DeanElec/Compact-high-efficiency-illumination-systems-for-in-orbit-microscopy/Lens-characterisation/resolving_power_and_chromatic_aberration/logistical_fit_red_green_blue_spectrums.PNG

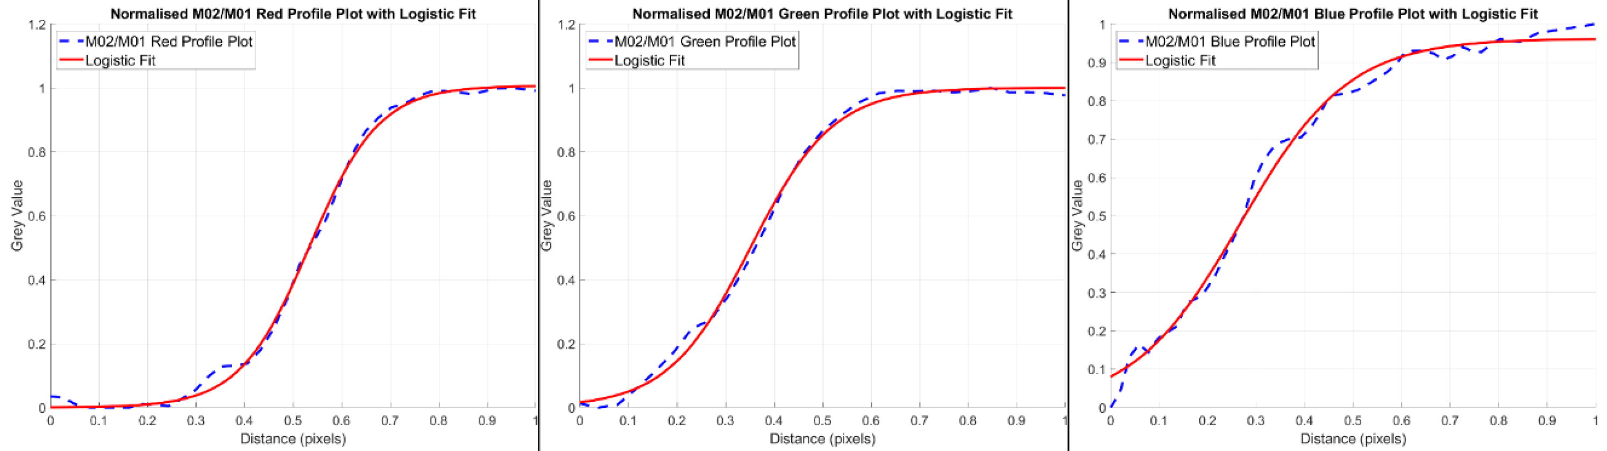
Lens-characterisation/resolving_power_and_chromatic_aberration/logistical_fit_red_green_blue_spectrums.PNG
