DeanElec/Compact-high-efficiency-illumination-systems-for-in-orbit-microscopy/Microscope_CAD_Designs/Microscope_CAD_Design_V2_Files/Step_Files/New_Spur_and_Rod v4.step

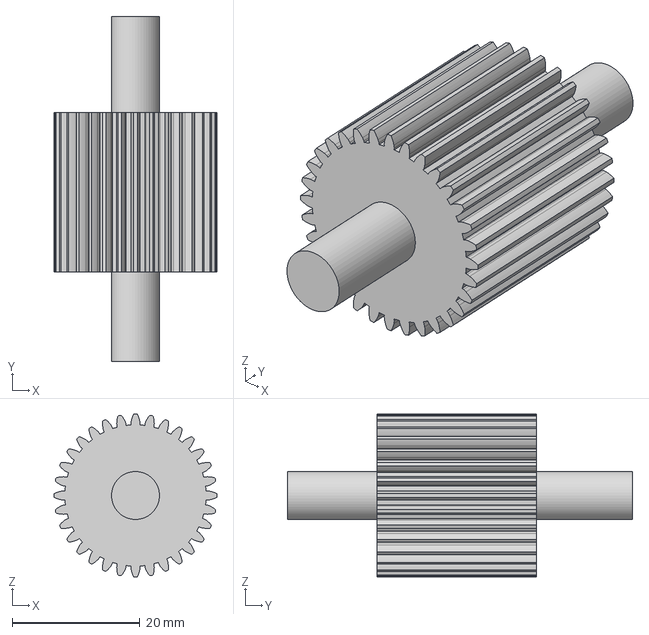
[picture p23: CAD file, 2024-05-28]
Microscope_CAD_Designs/Microscope_CAD_Design_V2_Files/Step_Files/New_Spur_and_Rod v4.step
25.5 x 54.0 x 25.5 mm
