DeanElec/Compact-high-efficiency-illumination-systems-for-in-orbit-microscopy/Microscope_CAD_Designs/Microscope_Stand_V1/Microscope_CAD_Design_V1_Files/Step_Files/Camera_Holder v3.step

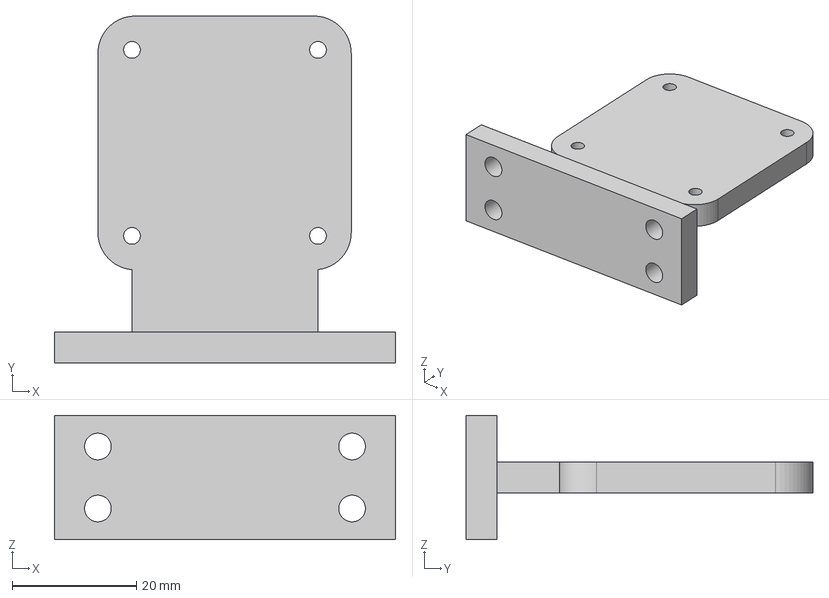
[picture p24: CAD file, 2024-05-28]
Microscope_CAD_Designs/Microscope_Stand_V1/Microscope_CAD_Design_V1_Files/Step_Files/Camera_Holder v3.step
55.0 x 56.0 x 20.0 mm
