DeanElec/Compact-high-efficiency-illumination-systems-for-in-orbit-microscopy/Microscope_CAD_Designs/Microscope_Stand_V1/Microscope_CAD_Design_V1_Files/Step_Files/Base Plate Dimensions v2.step

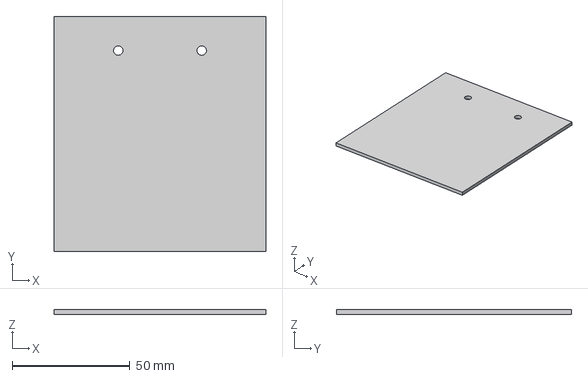
[picture p25: CAD file, 2024-05-28]
Microscope_CAD_Designs/Microscope_Stand_V1/Microscope_CAD_Design_V1_Files/Step_Files/Base Plate Dimensions v2.step
90.0 x 100.0 x 2.00 mm
