DeanElec/Compact-high-efficiency-illumination-systems-for-in-orbit-microscopy/Lens-characterisation/general_lens_characterisation_parameters/Lens kit chacterisation graph (2).png

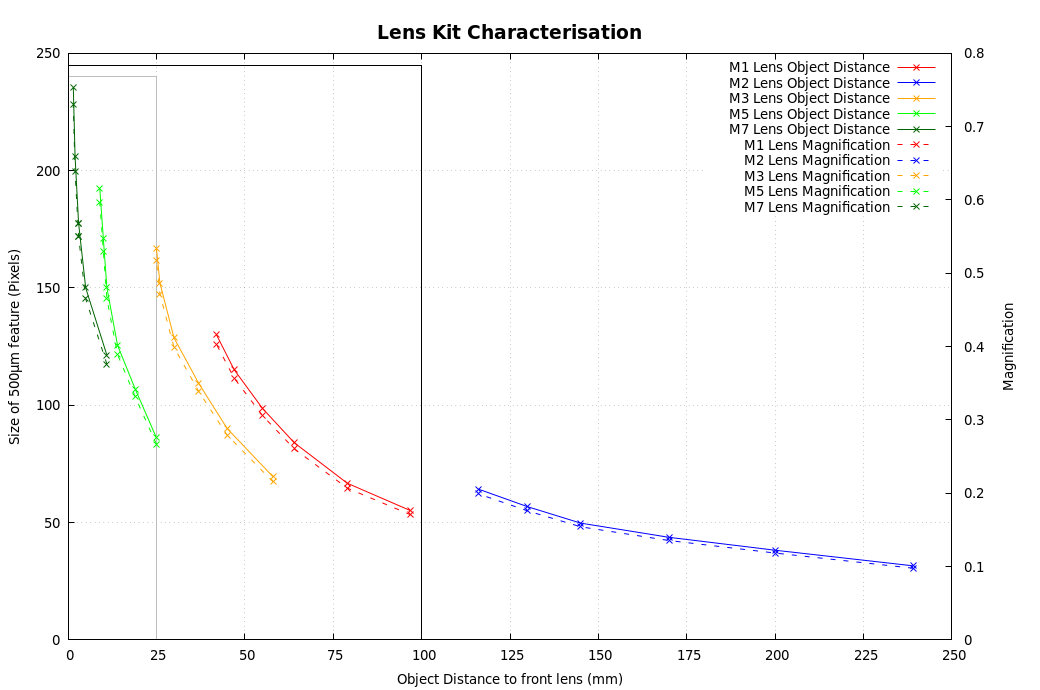
Lens-characterisation/general_lens_characterisation_parameters/Lens kit chacterisation graph (2).png
