DeanElec/Compact-high-efficiency-illumination-systems-for-in-orbit-microscopy/Lens-characterisation/general_lens_characterisation_parameters/Lens_Data_Object_Distance_vs_Measured_FOV.png

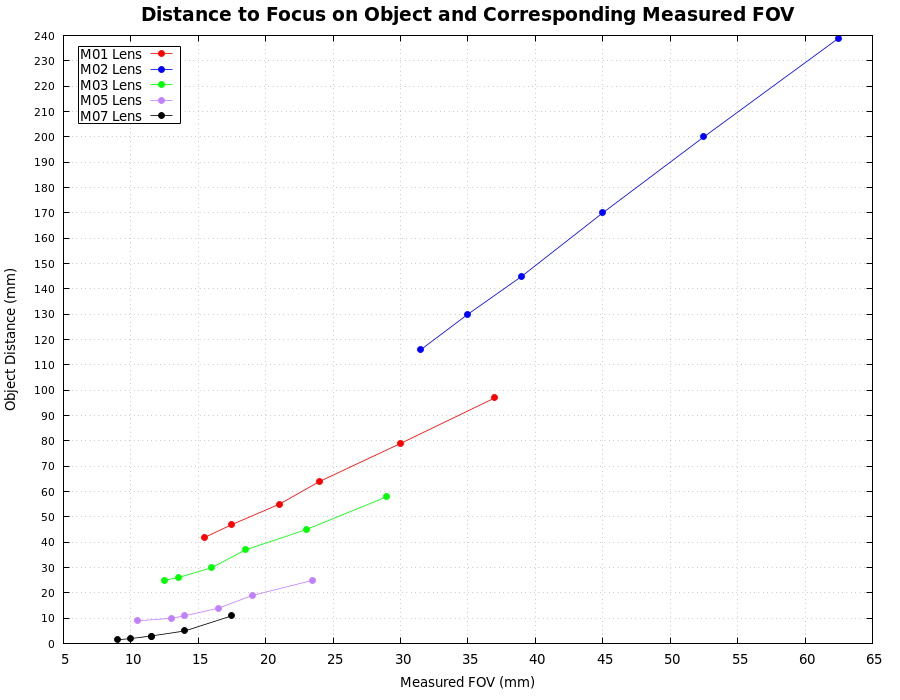
Lens-characterisation/general_lens_characterisation_parameters/Lens_Data_Object_Distance_vs_Measured_FOV.png
