DeanElec/Compact-high-efficiency-illumination-systems-for-in-orbit-microscopy/Lens-characterisation/general_lens_characterisation_parameters/linegraph_with_markers.png

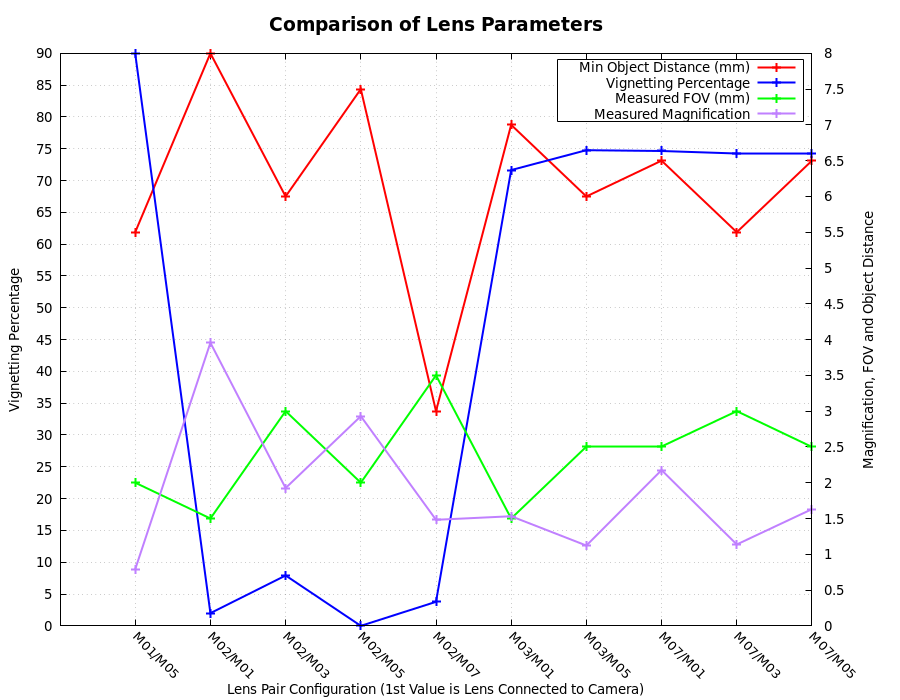
Lens-characterisation/general_lens_characterisation_parameters/linegraph_with_markers.png
