DeanElec/Compact-high-efficiency-illumination-systems-for-in-orbit-microscopy/Lens-characterisation/general_lens_characterisation_parameters/magnification_heatmap.png

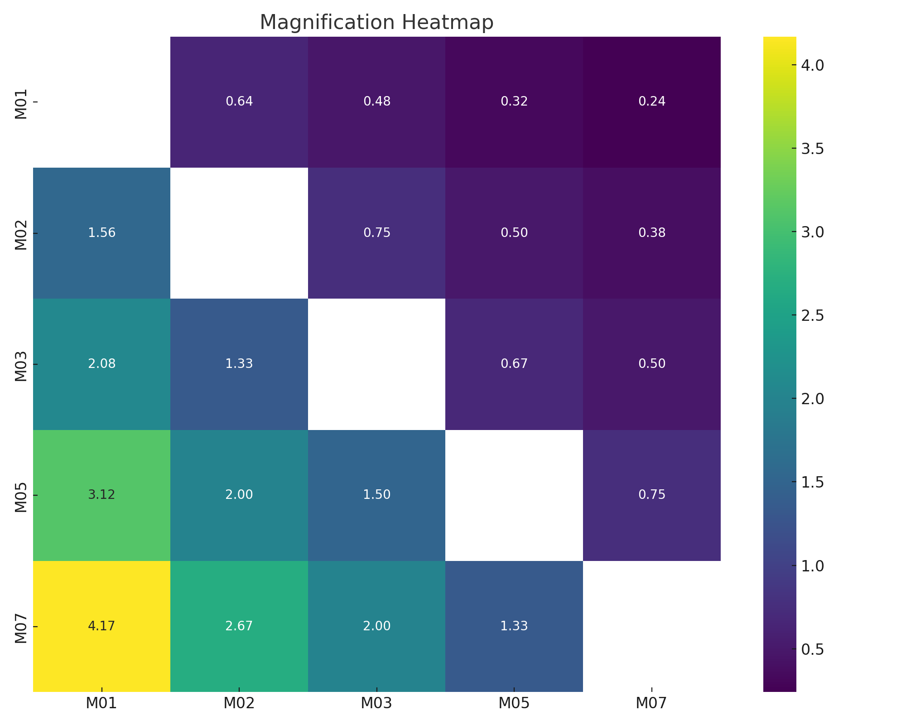
Lens-characterisation/general_lens_characterisation_parameters/magnification_heatmap.png
