DeanElec/Compact-high-efficiency-illumination-systems-for-in-orbit-microscopy/Lens-characterisation/light_transmission_efficiency/Capture.PNG

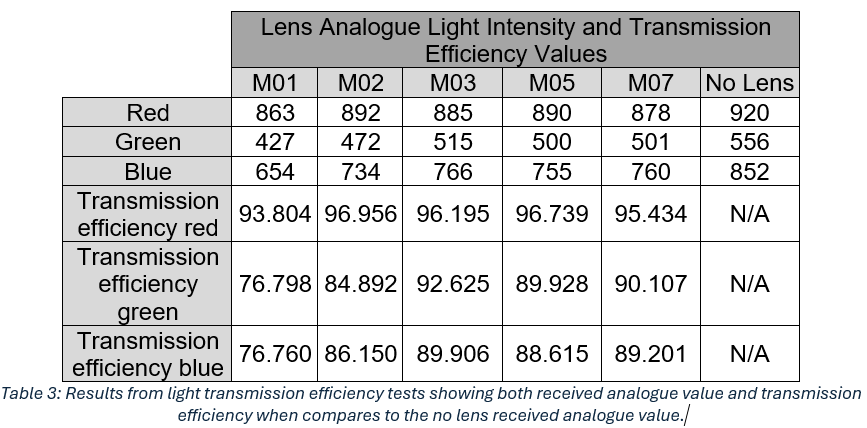
Lens-characterisation/light_transmission_efficiency/Capture.PNG
