DeanElec/Compact-high-efficiency-illumination-systems-for-in-orbit-microscopy/Lens-characterisation/light_transmission_efficiency/Internal_on_mount_side_of_lens_that_houses_LDR.png

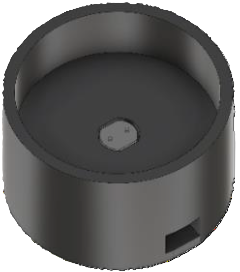
Lens-characterisation/light_transmission_efficiency/Internal_on_mount_side_of_lens_that_houses_LDR.png
