DeanElec/Compact-high-efficiency-illumination-systems-for-in-orbit-microscopy/Lens-characterisation/resolving_power_and_chromatic_aberration/M02_M01_Profile_Plots.png

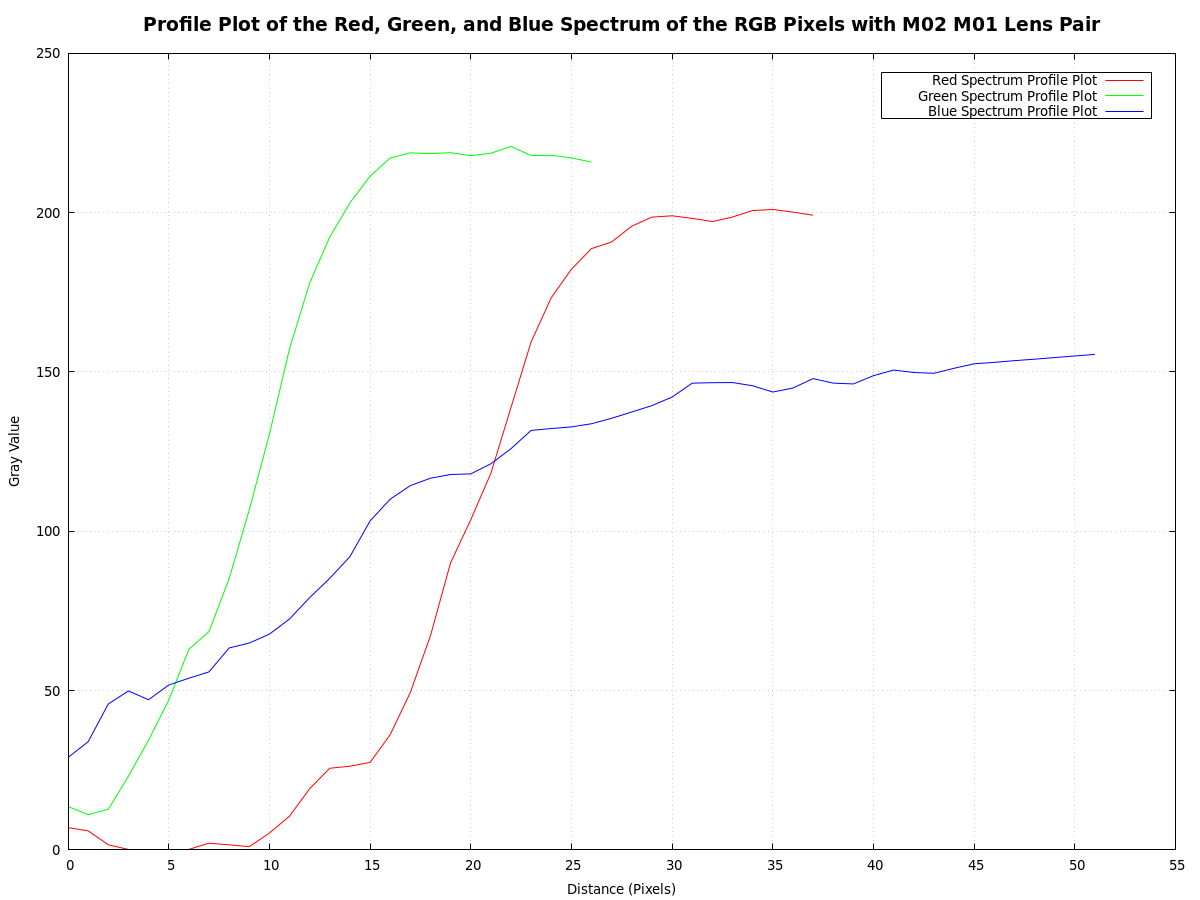
Lens-characterisation/resolving_power_and_chromatic_aberration/M02_M01_Profile_Plots.png
