DeanElec/Compact-high-efficiency-illumination-systems-for-in-orbit-microscopy/Lens-characterisation/resolving_power_and_chromatic_aberration/Parameter_of_RGB_Pixels_Samsung_Tab_S6_Lite_with_M02_M01_Lens_Pair.PNG

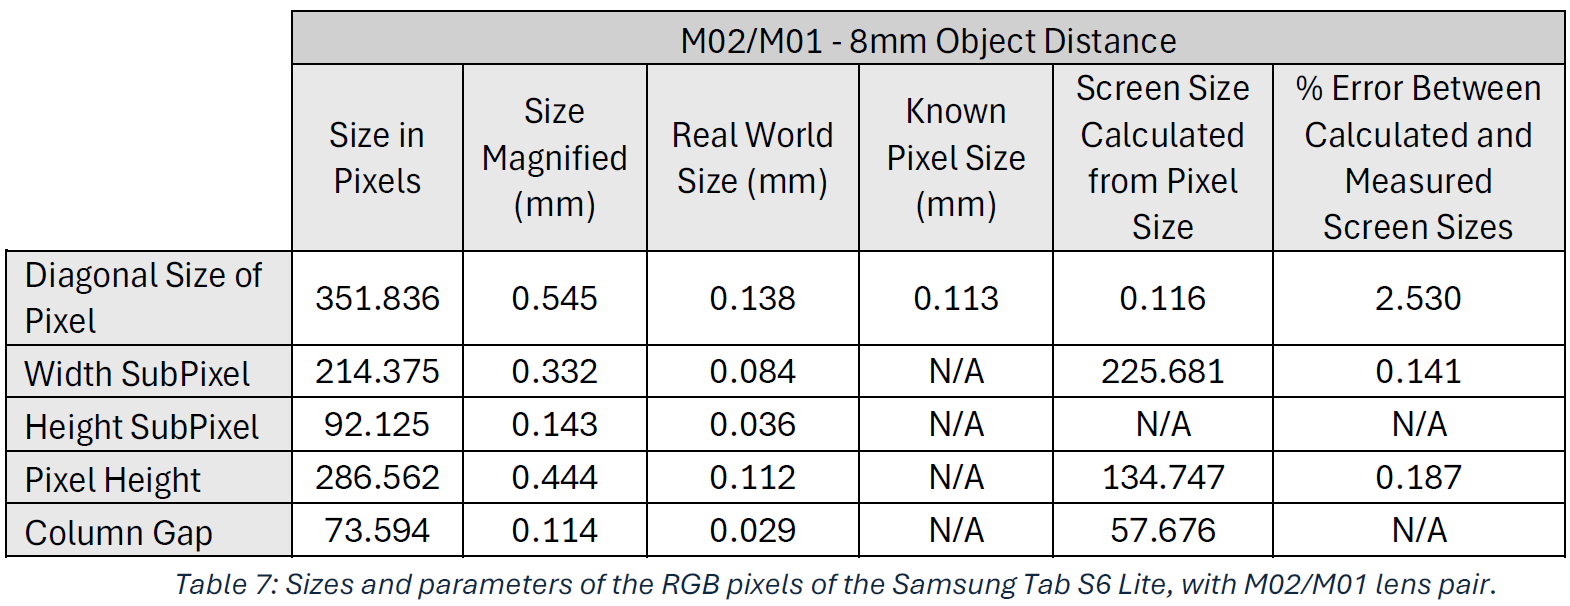
Lens-characterisation/resolving_power_and_chromatic_aberration/Parameter_of_RGB_Pixels_Samsung_Tab_S6_Lite_with_M02_M01_Lens_Pair.PNG
