DeanElec/Compact-high-efficiency-illumination-systems-for-in-orbit-microscopy/Lens-characterisation/resolving_power_and_chromatic_aberration/resolving_power_of_each_lens_config.PNG

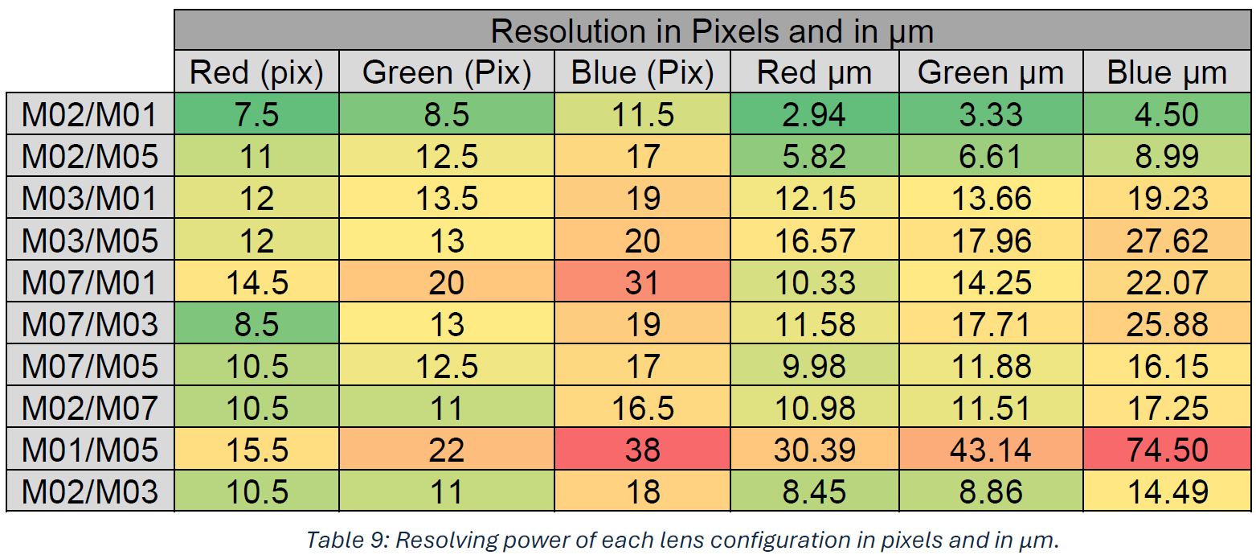
Lens-characterisation/resolving_power_and_chromatic_aberration/resolving_power_of_each_lens_config.PNG
