DeanElec/Compact-high-efficiency-illumination-systems-for-in-orbit-microscopy/Lens-characterisation/resolving_power_and_chromatic_aberration/summarised_rise_coefficent_from_logistical_fit.PNG

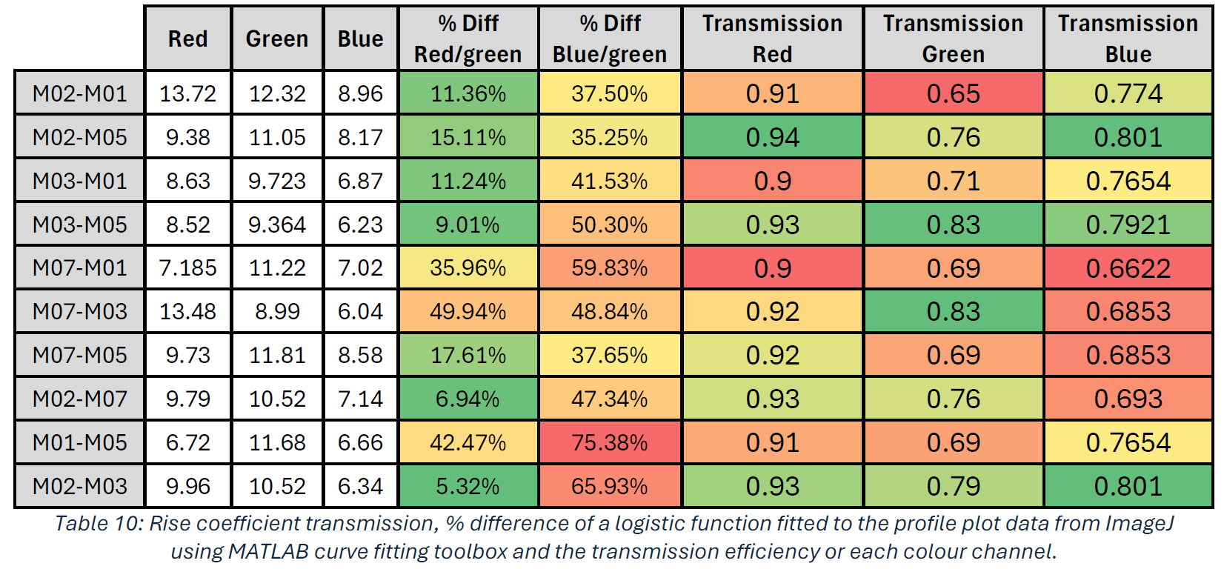
Lens-characterisation/resolving_power_and_chromatic_aberration/summarised_rise_coefficent_from_logistical_fit.PNG
