DeanElec/Compact-high-efficiency-illumination-systems-for-in-orbit-microscopy/Results/alignment_of_LED_ring_for_all_3_modalities.png

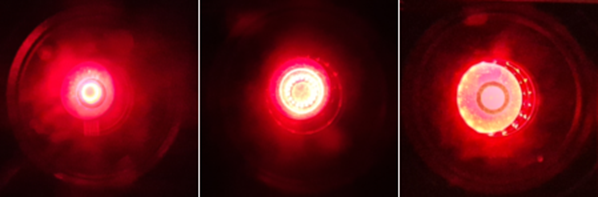
Results/alignment_of_LED_ring_for_all_3_modalities.png
