DeanElec/Compact-high-efficiency-illumination-systems-for-in-orbit-microscopy/Results/Buccal_Epithelial_Cells_3_Modes.png

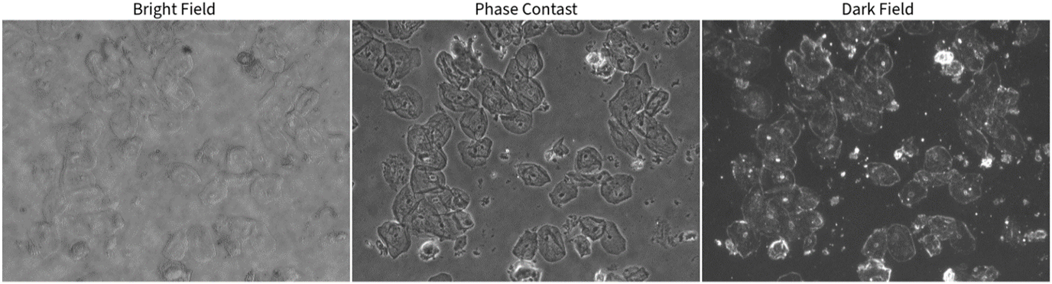
Results/Buccal_Epithelial_Cells_3_Modes.png
