DeanElec/Compact-high-efficiency-illumination-systems-for-in-orbit-microscopy/Results/Final_system_showing_how_images_are_taken.png

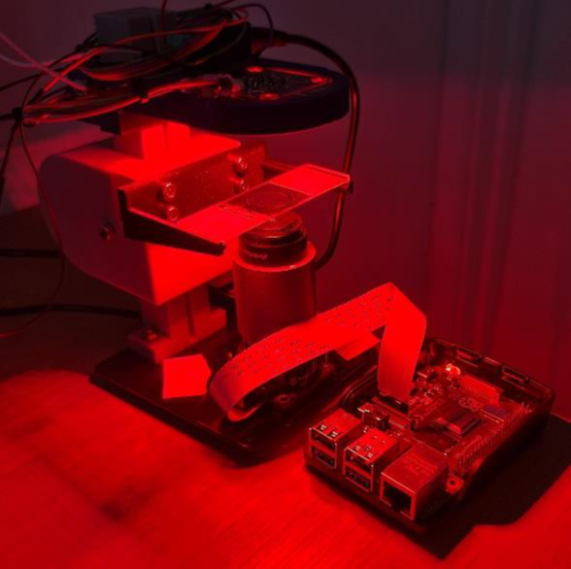
Results/Final_system_showing_how_images_are_taken.png
