DeanElec/Compact-high-efficiency-illumination-systems-for-in-orbit-microscopy/Results/normalised_logistic_fit_compared_to_profile_plot.png

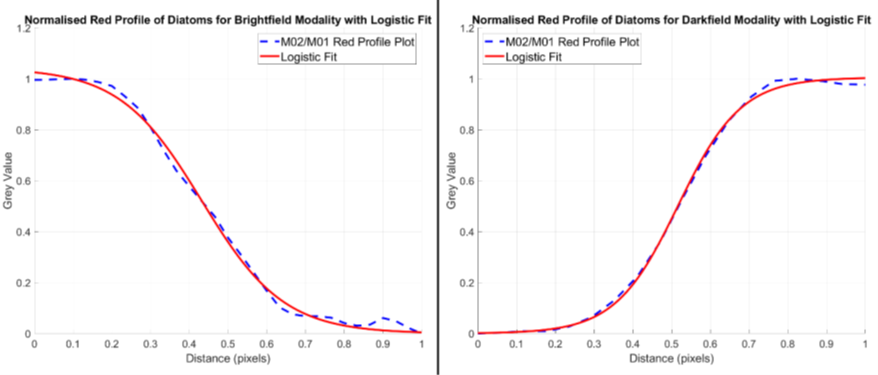
Results/normalised_logistic_fit_compared_to_profile_plot.png
