DeanElec/Compact-high-efficiency-illumination-systems-for-in-orbit-microscopy/Code/Raspberry Pi 4 Code/get_Time_test_main.cpp

#include <iostream>
#include "DateTime.h"
#include <string.h>

int main() {
    std::string test = DateTime::getInstance().getDateTime();
    // Output the date and time string
    std::cout << "Current date and time as string: " << test << std::endl;



    return 0;
}
